Seb7159/myHaum/web/form/map/img/2.jpg

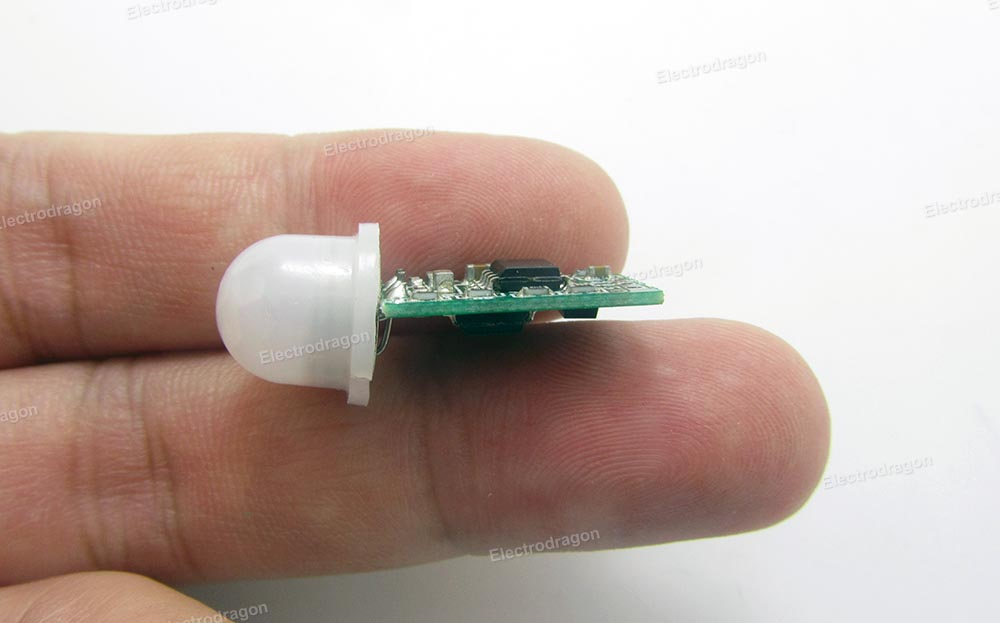
web/form/map/img/2.jpg
