Seb7159/myHaum/web/form/map/img/3.jpg

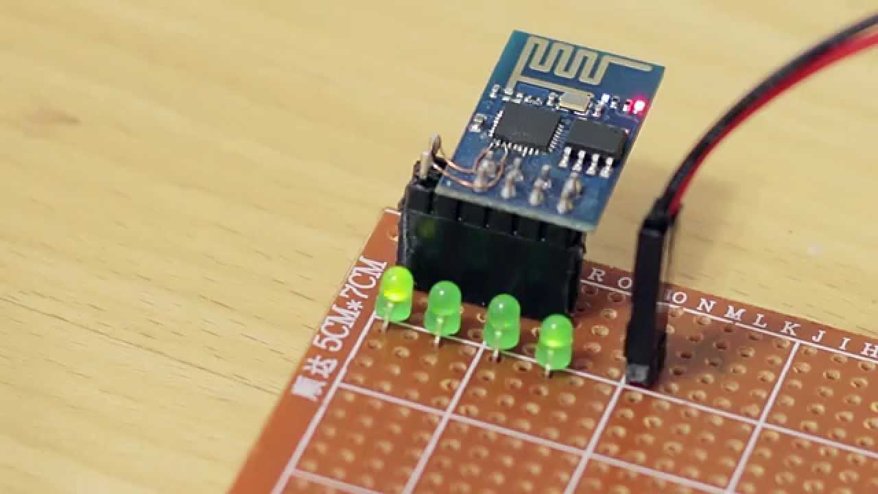
web/form/map/img/3.jpg
