Seb7159/myHaum/web/form/map/img/4.jpg

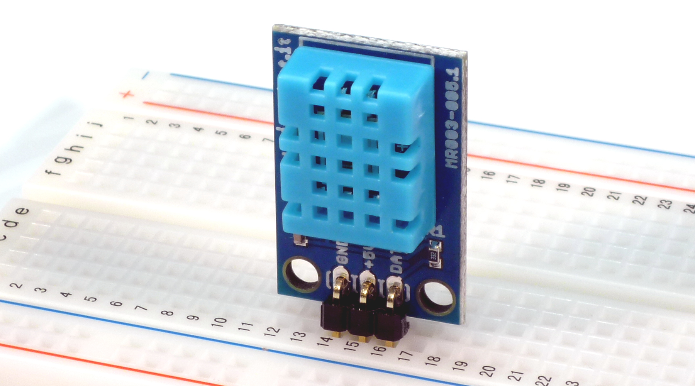
web/form/map/img/4.jpg
