Seb7159/myHaum/web/form/map/img/5.jpg

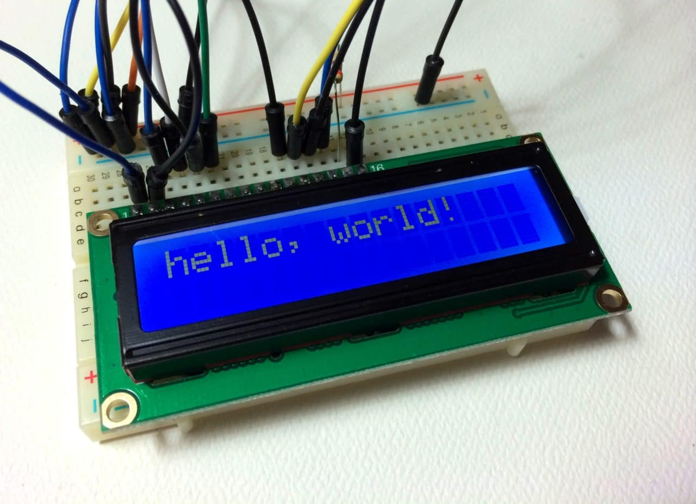
web/form/map/img/5.jpg
