Seb7159/myHaum/web/form/map/img/7.jpg

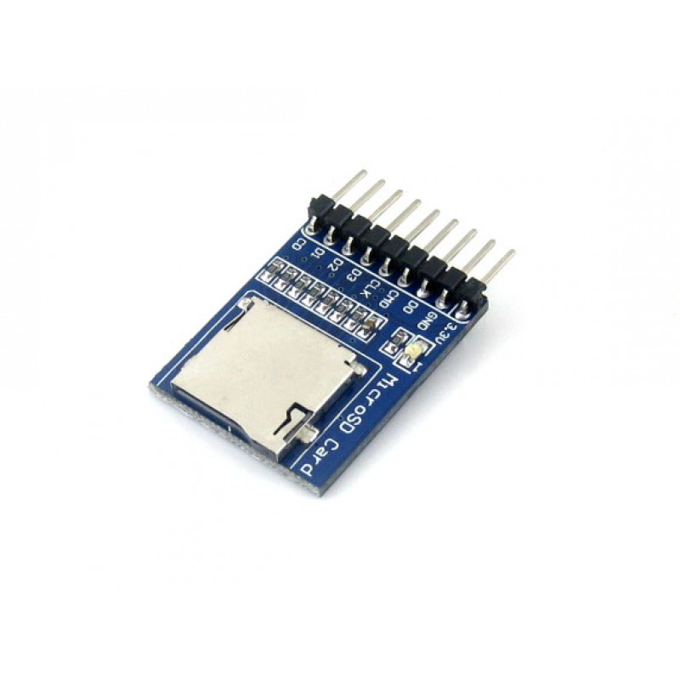
web/form/map/img/7.jpg
