Seb7159/myHaum/web/form/map/img/8.jpg

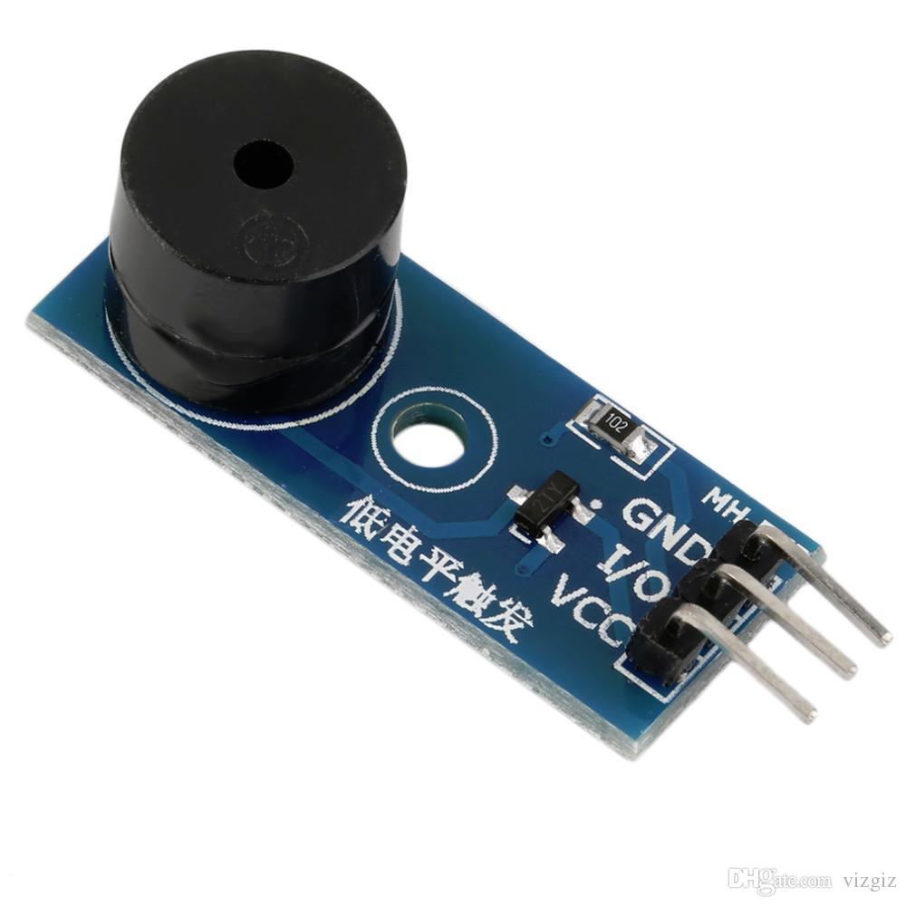
web/form/map/img/8.jpg
