Seb7159/myHaum/web/form/map/img/11.jpg

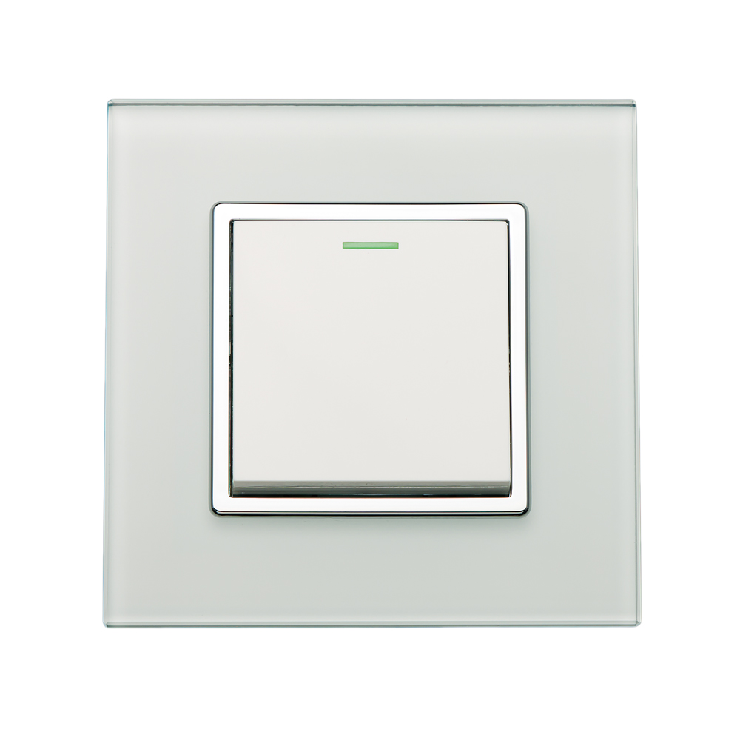
web/form/map/img/11.jpg
