Seb7159/myHaum/web/img/1.jpg

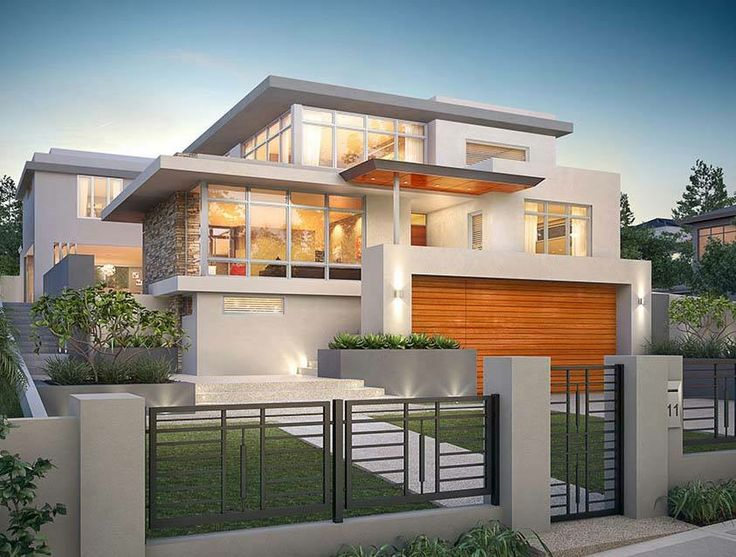
web/img/1.jpg
