Seb7159/myHaum/web/img/2.jpg

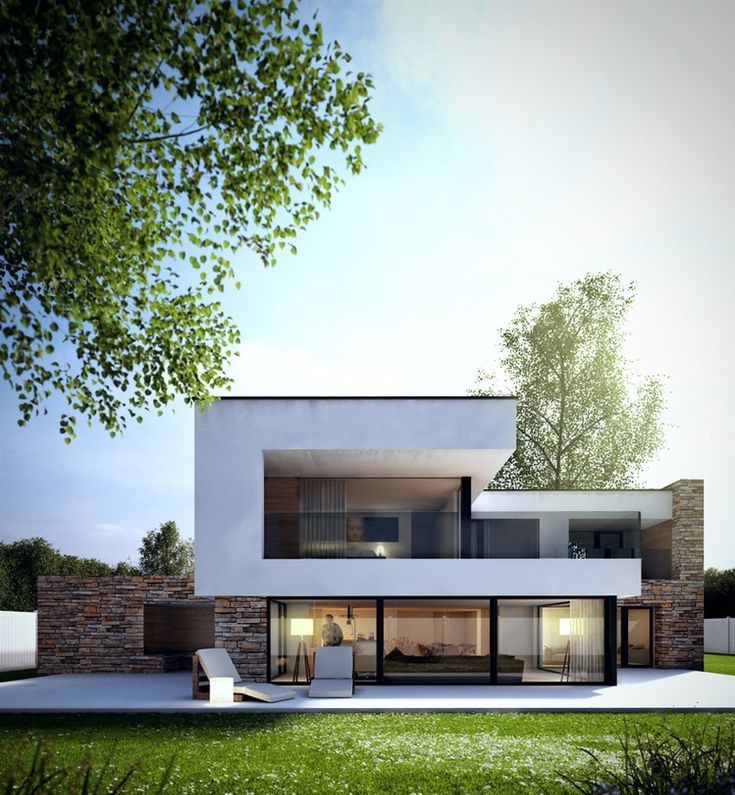
web/img/2.jpg
