Seb7159/myHaum/web/img/3.jpg

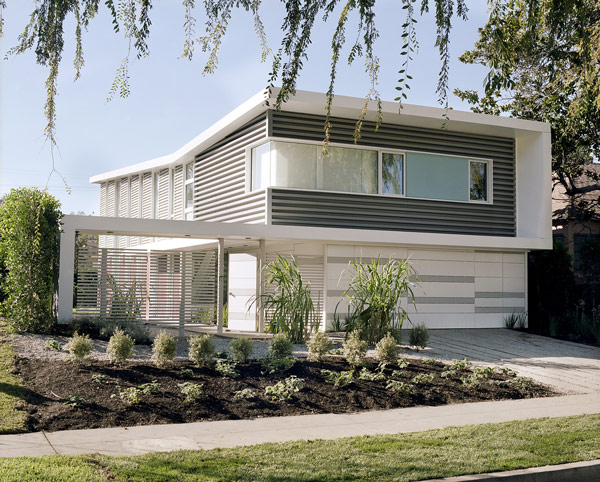
web/img/3.jpg
