Seb7159/myHaum/web/img/5.jpg

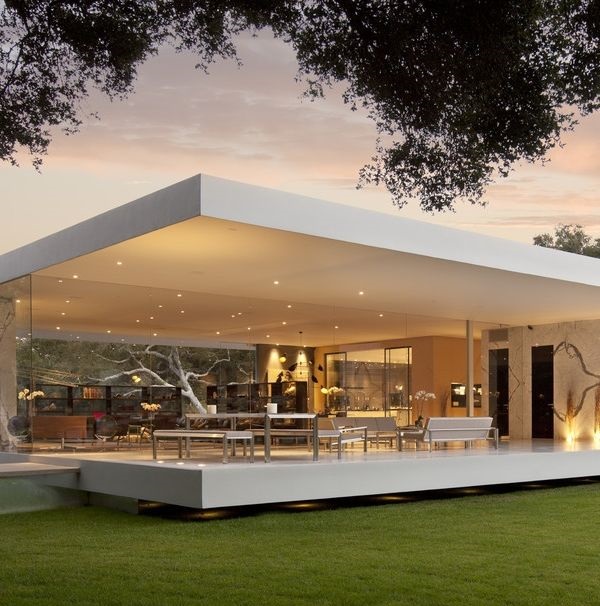
web/img/5.jpg
